darksonic2112/BOXX-Type-Controller/DARKSONIC BOXX/Letters/DA_SON.stl

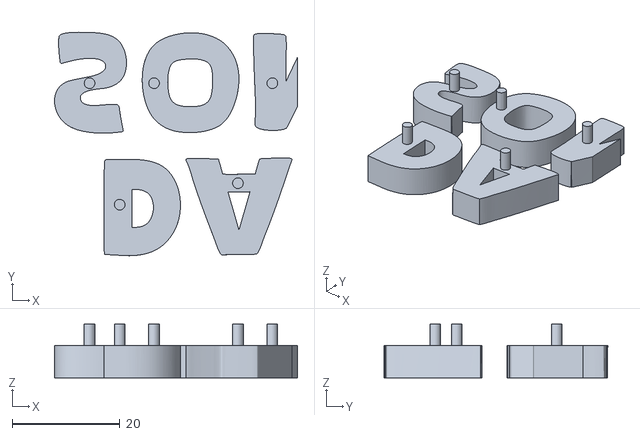
[picture p19: CAD file, 2024-08-22]
DARKSONIC BOXX/Letters/DA_SON.stl
45.2 x 41.6 x 10.0
