darksonic2112/BOXX-Type-Controller/Modular Components/Support_Beam.stl

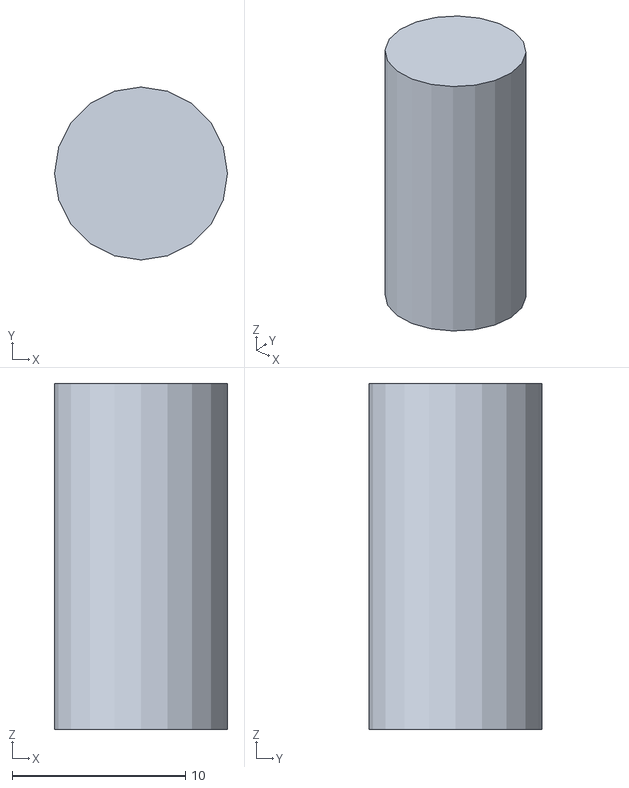
[picture p20: CAD file, 2024-08-22]
Modular Components/Support_Beam.stl
10.0 x 10.0 x 20.0
