darksonic2112/BOXX-Type-Controller/DARKSONIC BOXX/Letters/S.stl

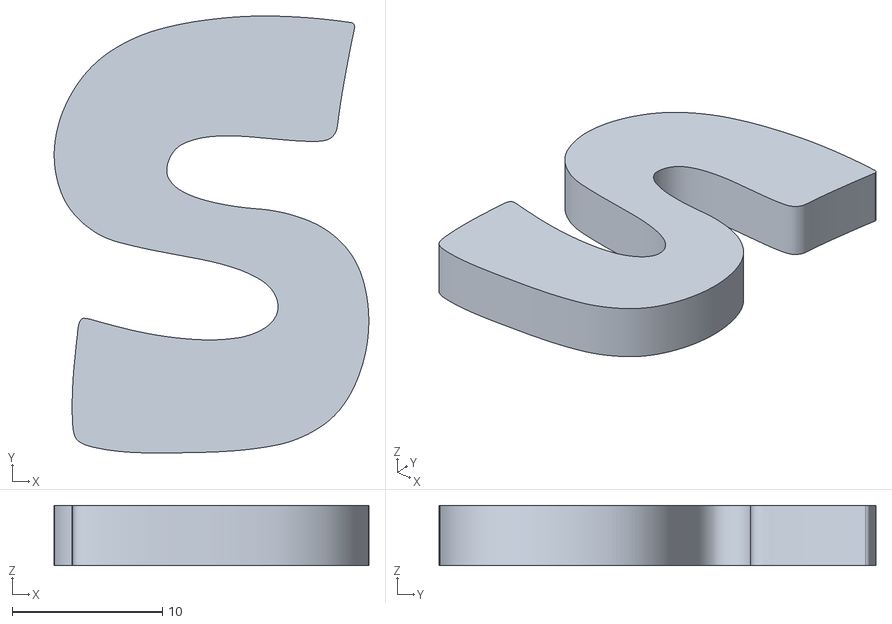
[picture p21: CAD file, 2024-08-22]
DARKSONIC BOXX/Letters/S.stl
20.9 x 29.1 x 4.00
