darksonic2112/BOXX-Type-Controller/DARKSONIC BOXX/Letters/I.stl

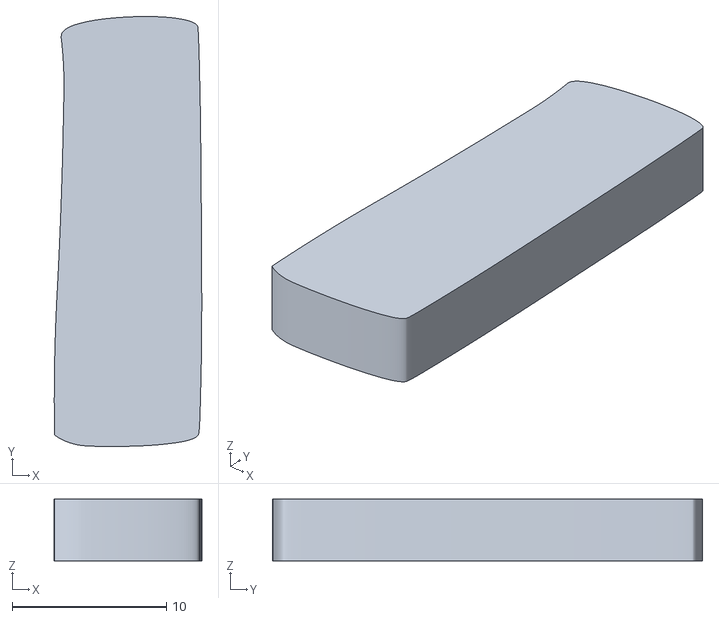
[picture p22: CAD file, 2024-08-22]
DARKSONIC BOXX/Letters/I.stl
9.56 x 27.9 x 4.00
