darksonic2112/BOXX-Type-Controller/DARKSONIC BOXX/Letters/D.stl

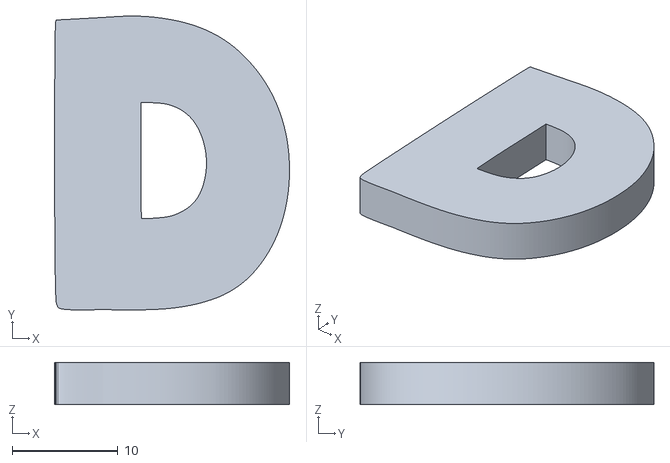
[picture p23: CAD file, 2024-08-22]
DARKSONIC BOXX/Letters/D.stl
22.2 x 27.8 x 4.00
