darksonic2112/BOXX-Type-Controller/DARKSONIC BOXX/Letters/RK_NIC.stl

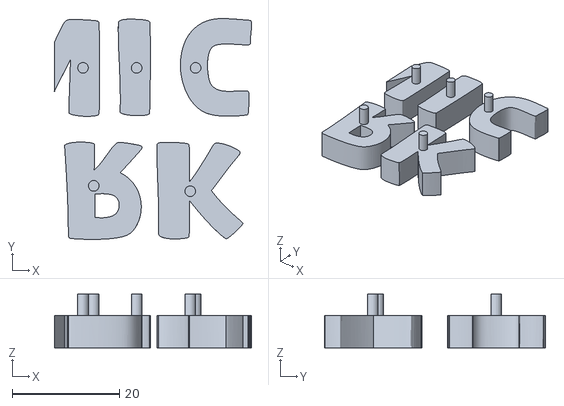
[picture p24: CAD file, 2024-08-22]
DARKSONIC BOXX/Letters/RK_NIC.stl
36.7 x 41.2 x 10.0
