darksonic2112/BOXX-Type-Controller/DARKSONIC BOXX/Letters/A.stl

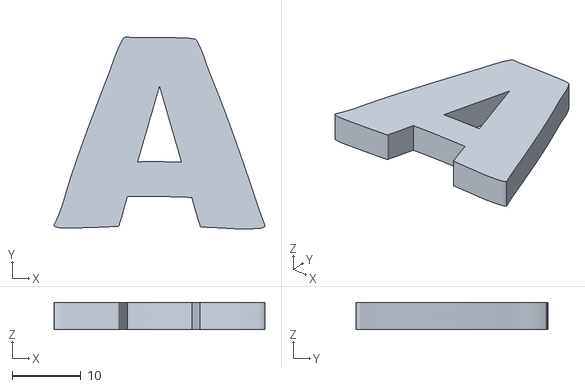
[picture p25: CAD file, 2024-08-22]
DARKSONIC BOXX/Letters/A.stl
30.7 x 28.0 x 4.00
